gregdavill/led-shades/hw/outputs/mcad/textures/ledGlasses_front_green.png

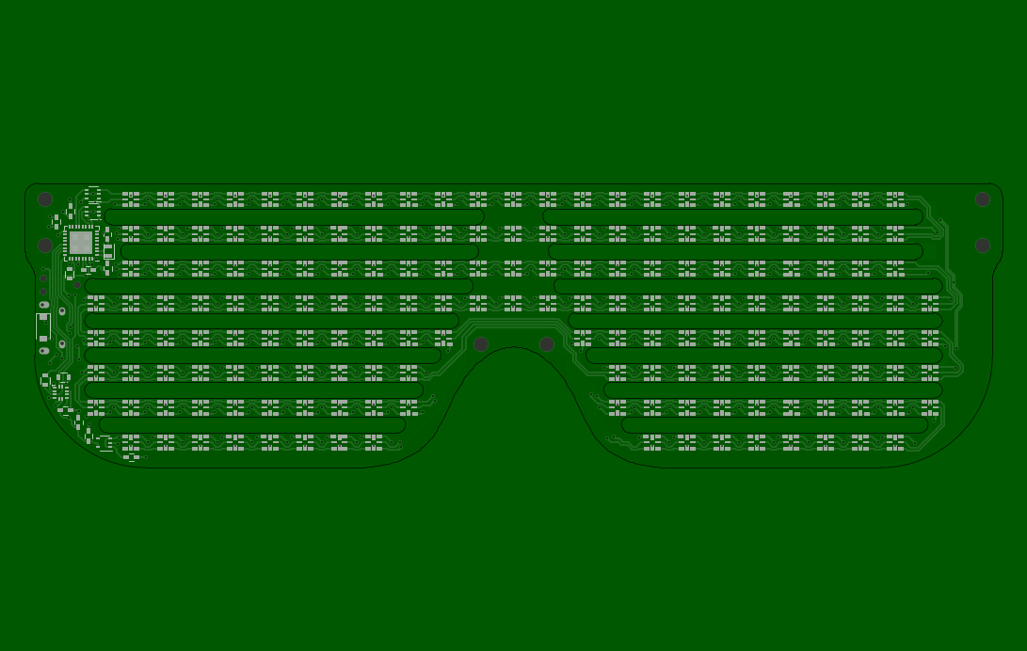
hw/outputs/mcad/textures/ledGlasses_front_green.png
