gregdavill/led-shades/hw/outputs/renders/Glasses_green.png

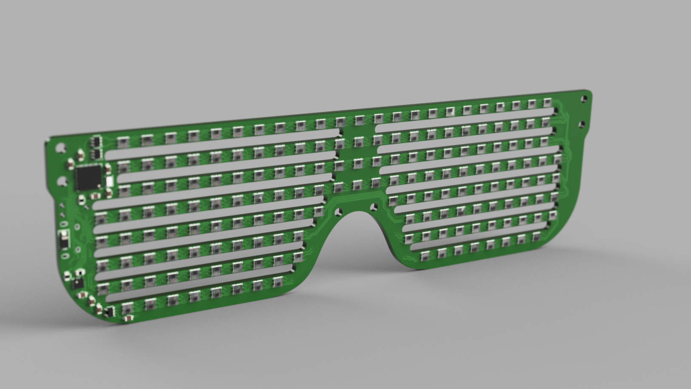
hw/outputs/renders/Glasses_green.png
