gregdavill/led-shades/hw/outputs/renders/Glasses_white.png

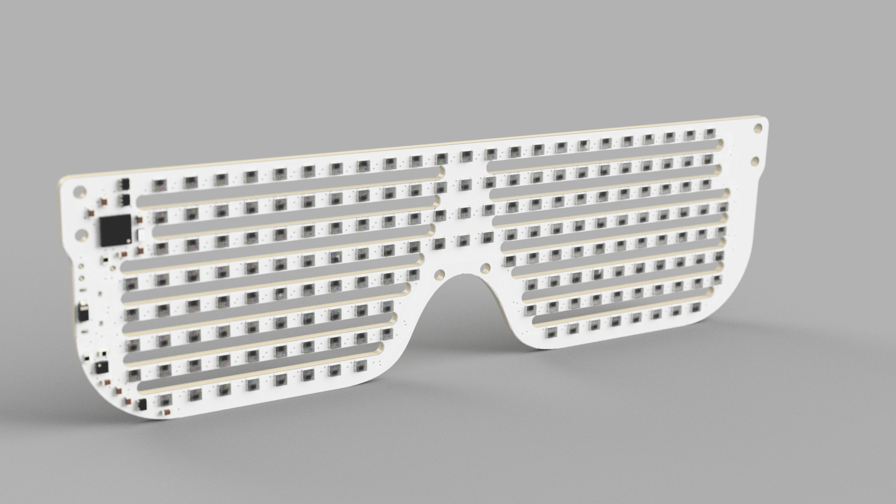
hw/outputs/renders/Glasses_white.png
